huangyuxin1217/Portable-outdoor-power-supply/Paper Sculpture Lamp Design/png/5.png

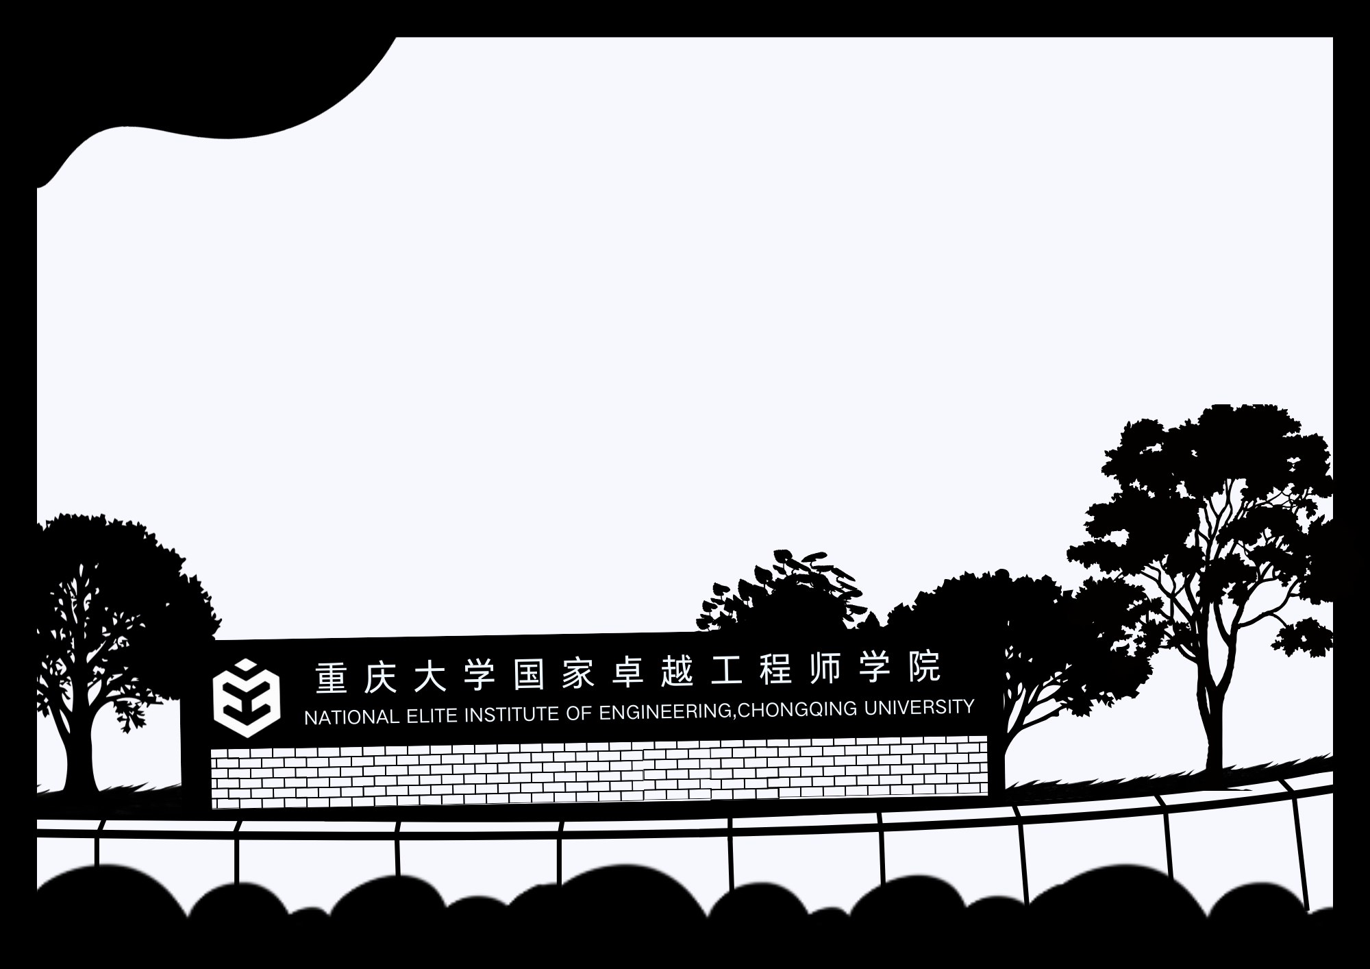
Paper Sculpture Lamp Design/png/5.png
